xKoney/myKerbalSimpit/STL/Top Panel v6 - B.stl

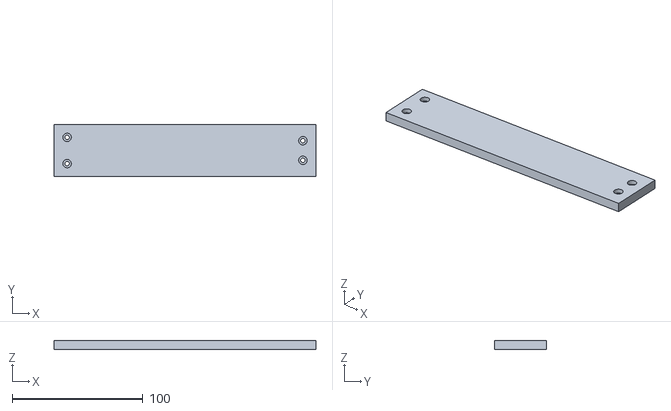
[picture p17: CAD file, 2024-05-05]
STL/Top Panel v6 - B.stl
200.0 x 40.0 x 6.53
