xKoney/myKerbalSimpit/STL/Rear Panel v10 - A.stl

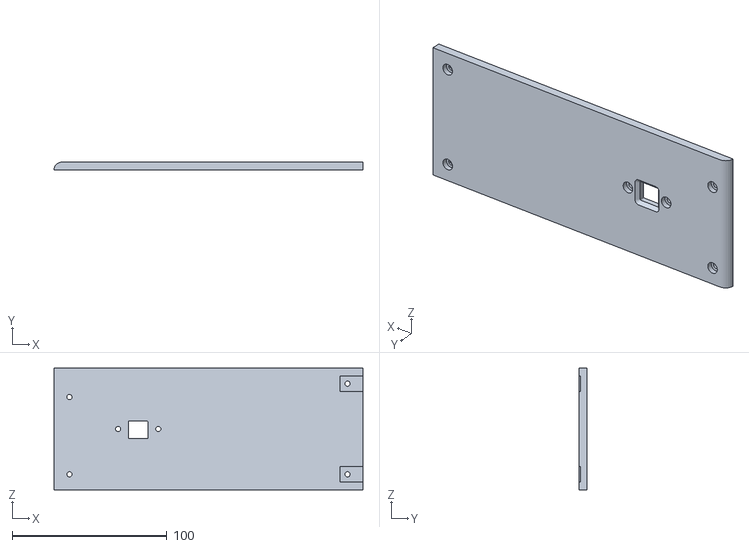
[picture p18: CAD file, 2024-05-05]
STL/Rear Panel v10 - A.stl
200.0 x 5.00 x 78.7
