xKoney/myKerbalSimpit/STL/Bottom Brace v13.stl

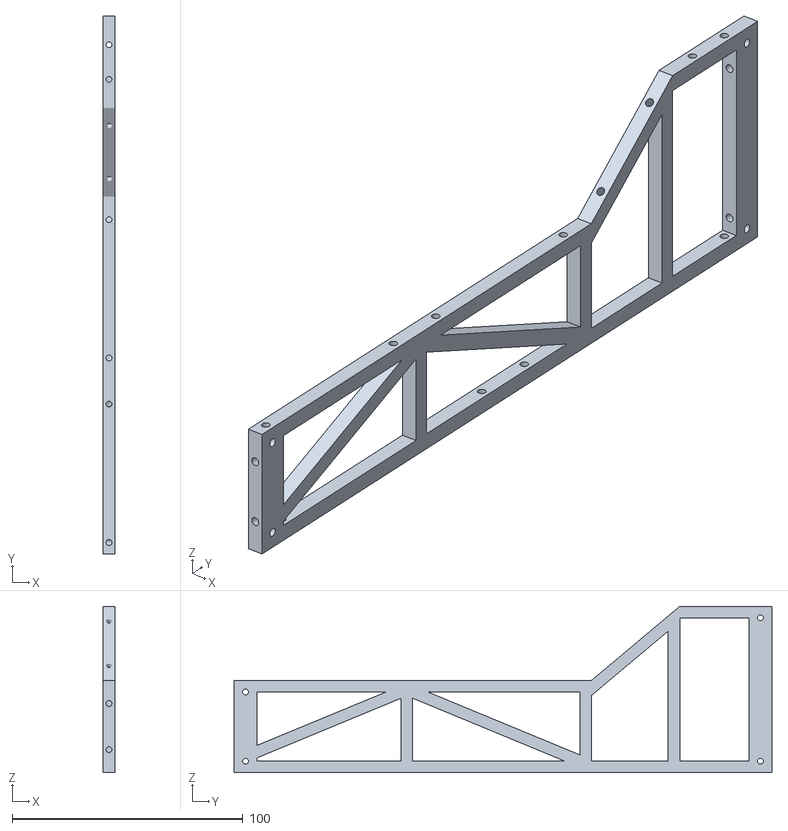
[picture p19: CAD file, 2024-05-05]
STL/Bottom Brace v13.stl
5.00 x 233.3 x 72.1
