xKoney/myKerbalSimpit/STL/Joystick Panel v11.stl

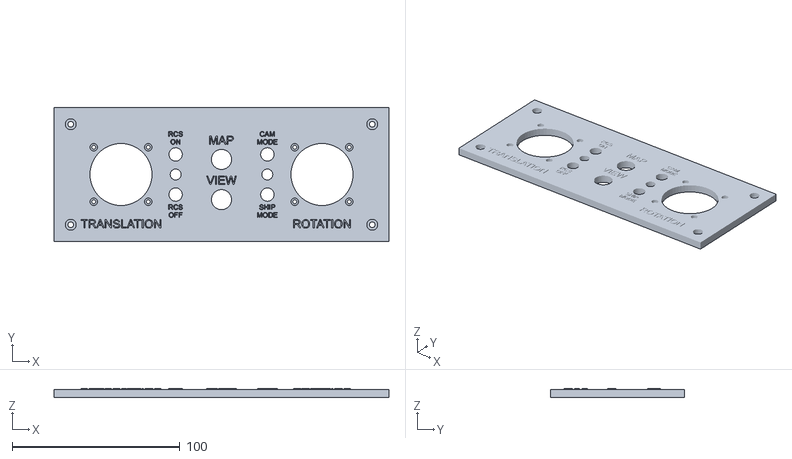
[picture p20: CAD file, 2024-05-05]
STL/Joystick Panel v11.stl
200.0 x 80.0 x 5.60
