xKoney/myKerbalSimpit/STL/Combo Brace 2 v7.stl

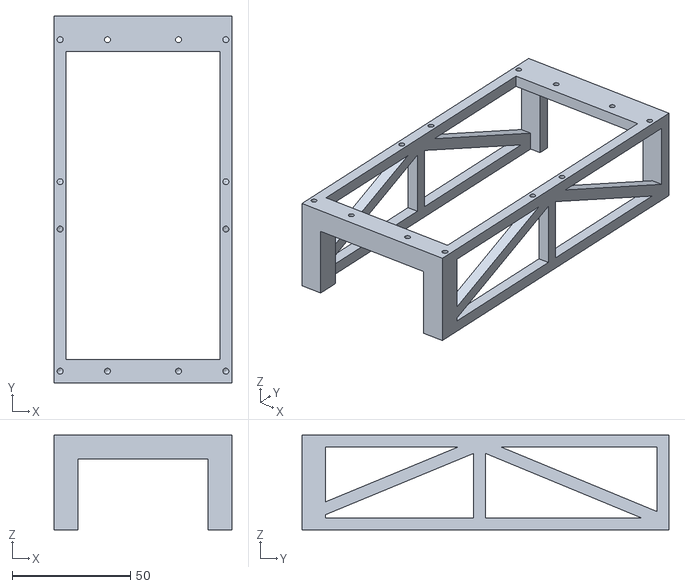
[picture p21: CAD file, 2024-05-05]
STL/Combo Brace 2 v7.stl
75.0 x 155.0 x 40.0
